danielskowronski/esp32-window-light-sensor/software/esp32-window-light-sensor/Identify.h

struct Identify : Service::AccessoryInformation {
  int nBlinks;
  SpanCharacteristic *identify;
  
  Identify(const char *name, const char *manu, const char *sn, const char *model, const char *version, int nBlinks) : Service::AccessoryInformation(){
    new Characteristic::Name(name);
    new Characteristic::Manufacturer(manu);
    new Characteristic::SerialNumber(sn);    
    new Characteristic::Model(model);
    new Characteristic::FirmwareRevision(version);
    identify=new Characteristic::Identify();

    this->nBlinks=nBlinks;

    pinMode(homeSpan.getStatusPin(),OUTPUT);
  }

  boolean update(){
    for(int i=0;i<nBlinks;i++){
      digitalWrite(homeSpan.getStatusPin(),LOW);
      delay(250);
      digitalWrite(homeSpan.getStatusPin(),HIGH);
      delay(250);
    }

    return(true);
  }
};
